Ronapa/Circuitos2/Imagenes/esquematico_margen_fase.PNG

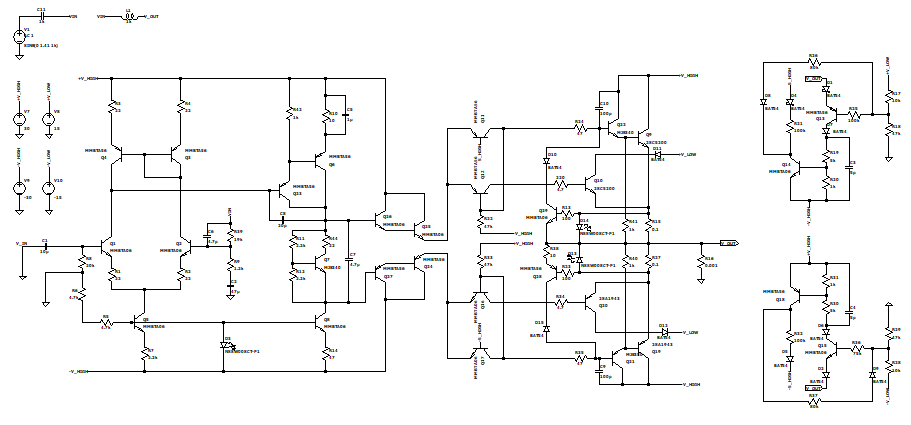
Imagenes/esquematico_margen_fase.PNG
