Ronapa/Circuitos2/Imagenes/grafico_compensacion.PNG

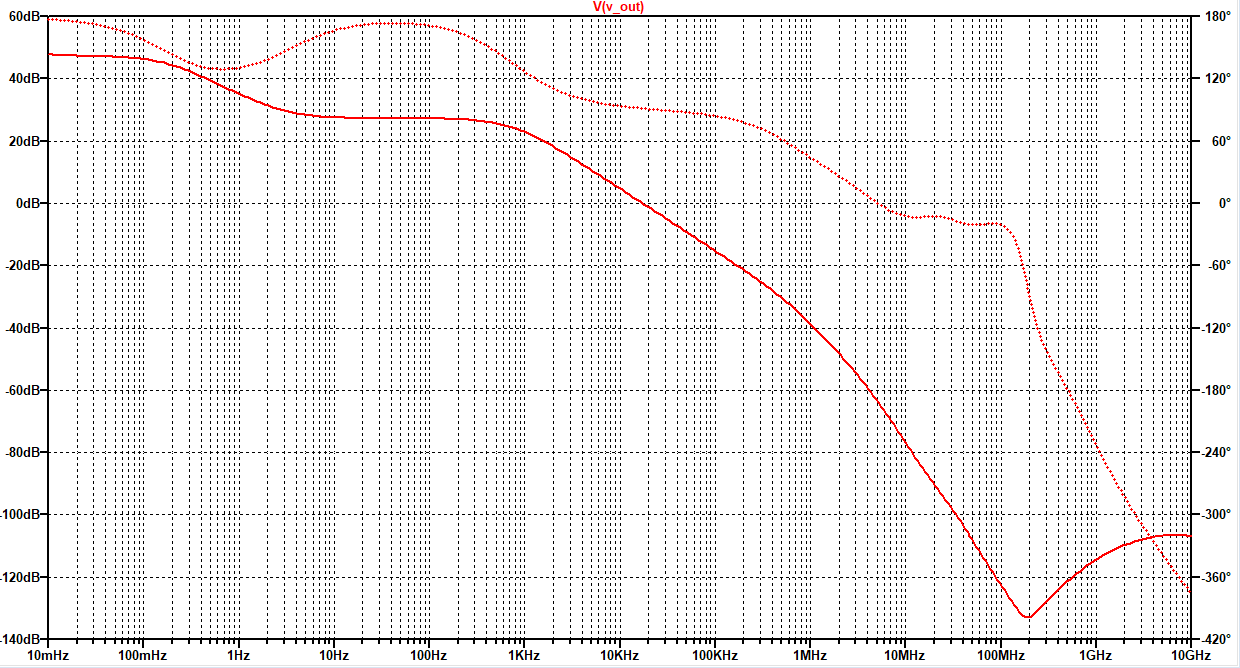
Imagenes/grafico_compensacion.PNG
