Ronapa/Circuitos2/Imagenes/Multiplicador_Vbe.PNG

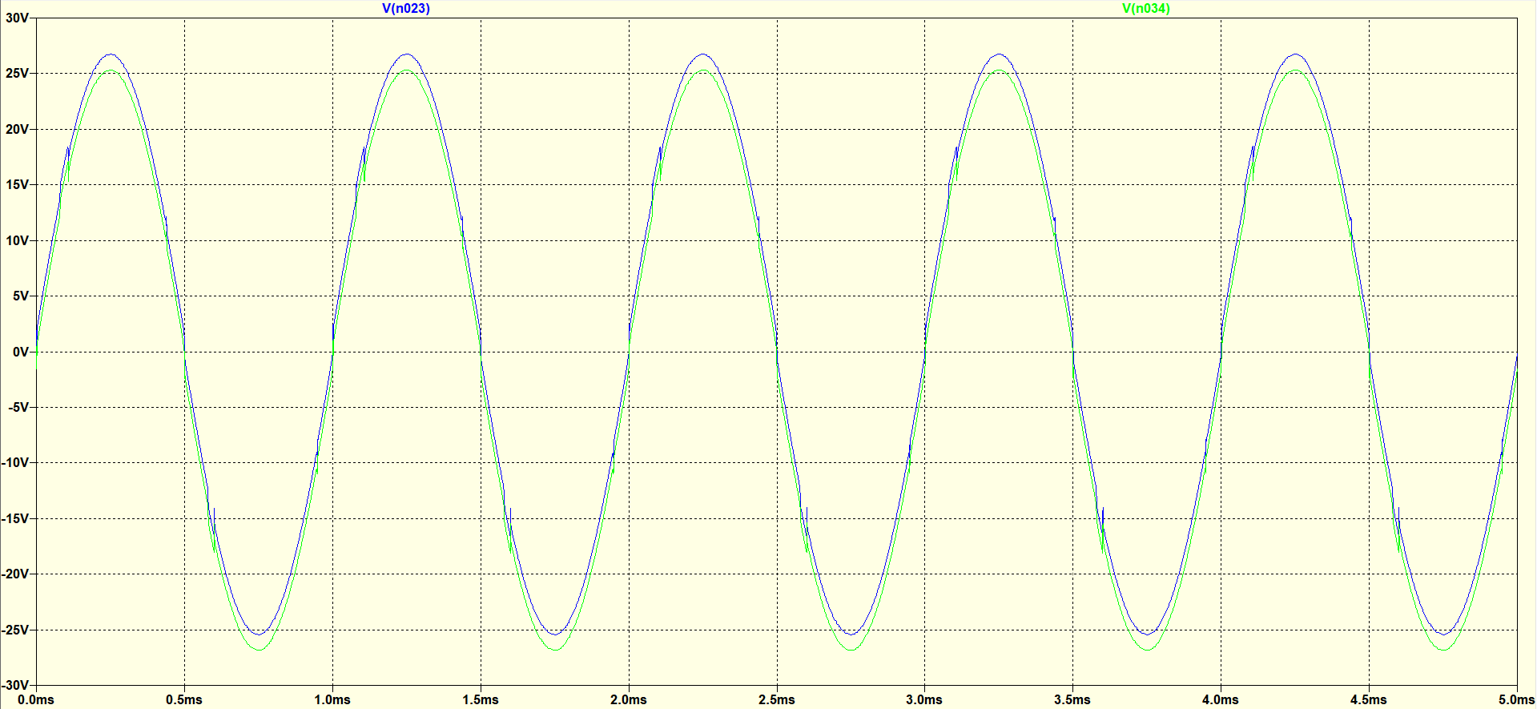
Imagenes/Multiplicador_Vbe.PNG
