Ronapa/Circuitos2/Imagenes/Tensión entrada.jpg

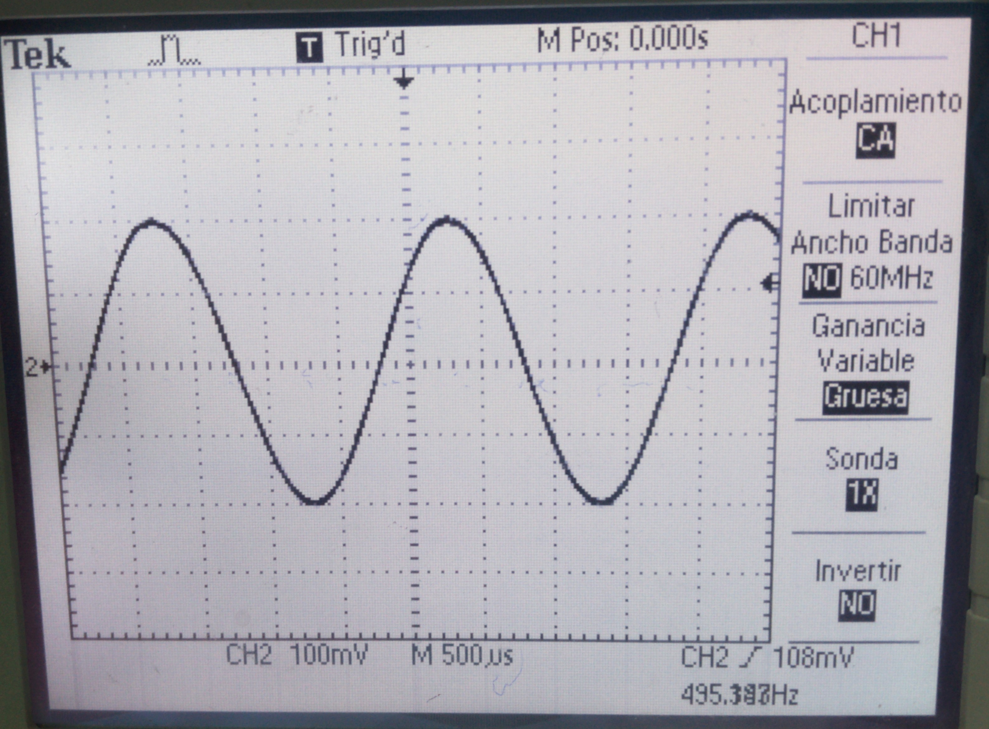
Imagenes/Tensión entrada.jpg
