Ronapa/Circuitos2/Imagenes/Tensión salida.jpg

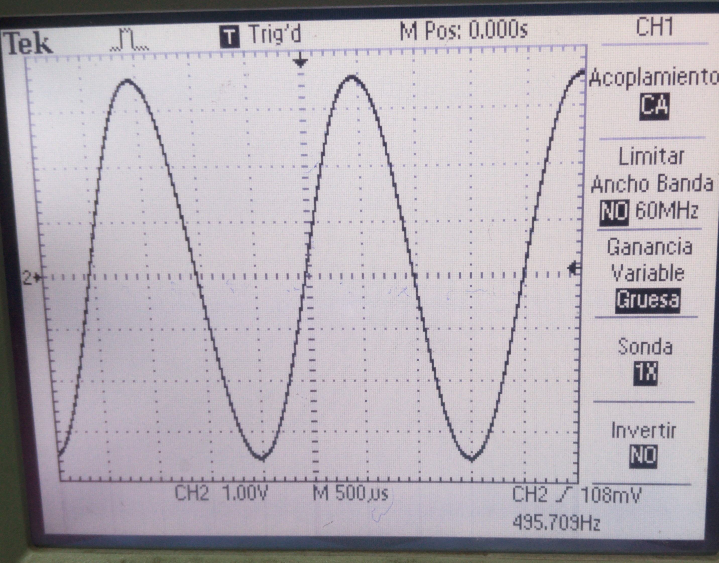
Imagenes/Tensión salida.jpg
