Ronapa/Circuitos2/PCB/Esquematico.PNG

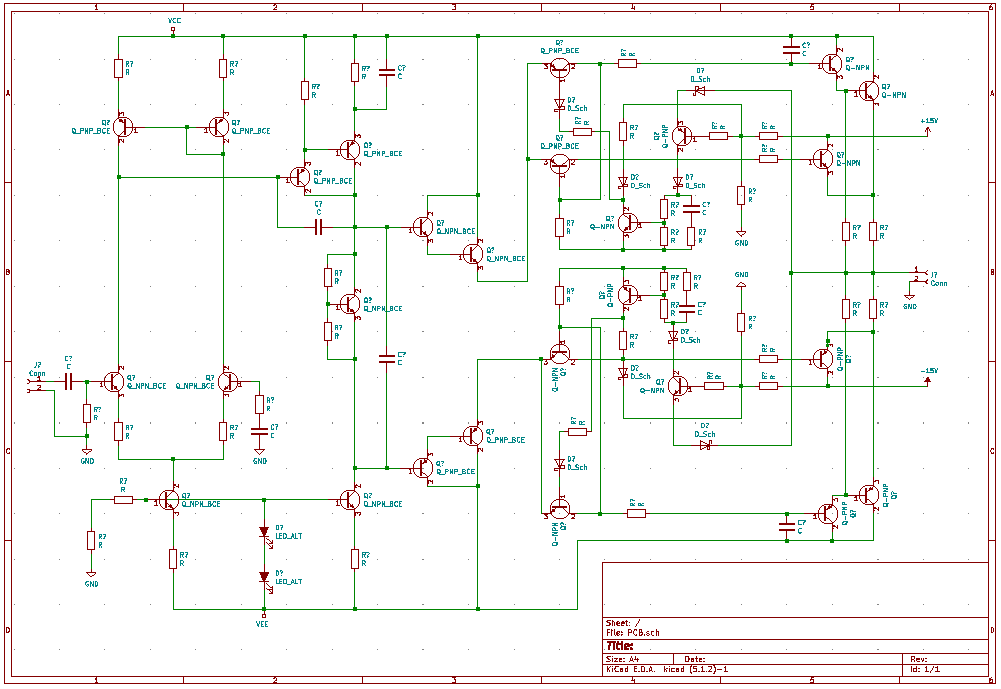
PCB/Esquematico.PNG
