Ronapa/Circuitos2/Simulaciones/fft 0.6V.PNG

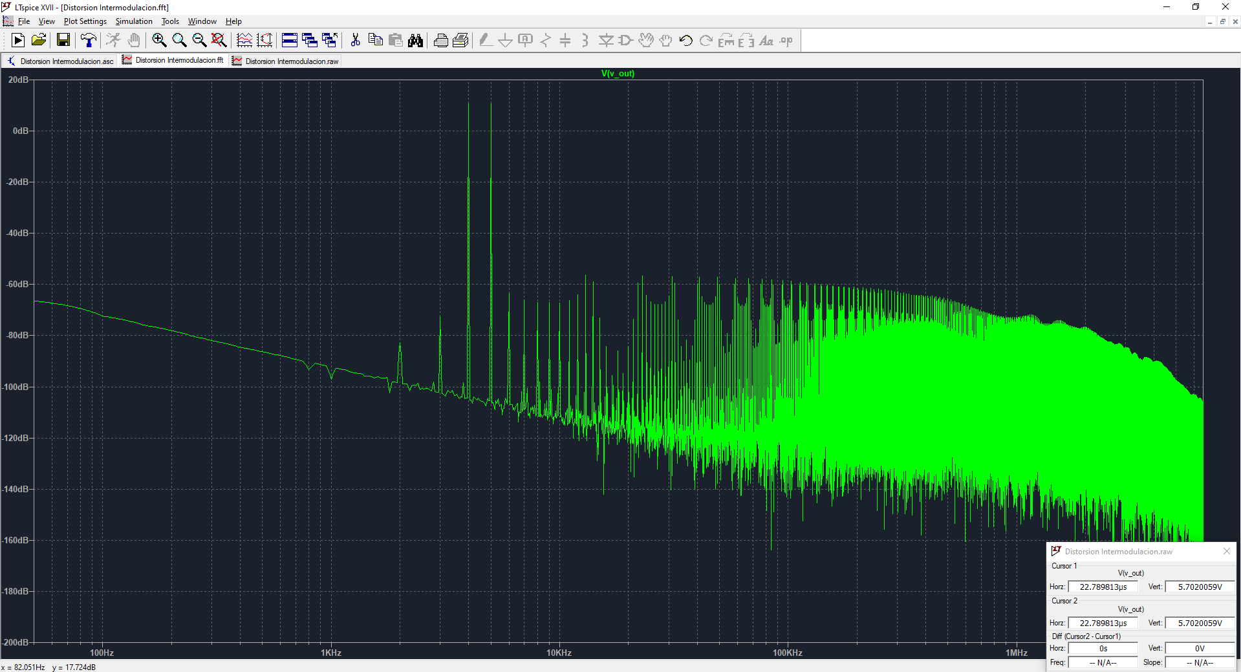
Simulaciones/fft 0.6V.PNG
