Ronapa/Circuitos2/Simulaciones/fft 1.4V 19 20k.PNG

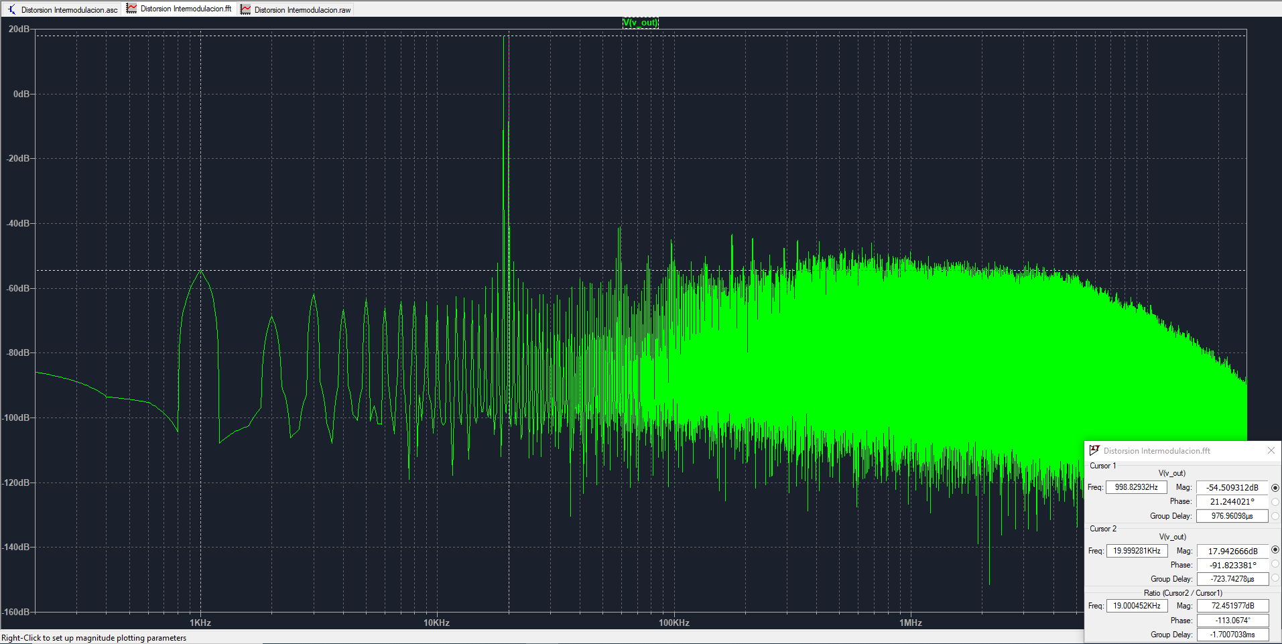
Simulaciones/fft 1.4V 19 20k.PNG
