Ronapa/Circuitos2/Simulaciones/fft 1.4V.PNG

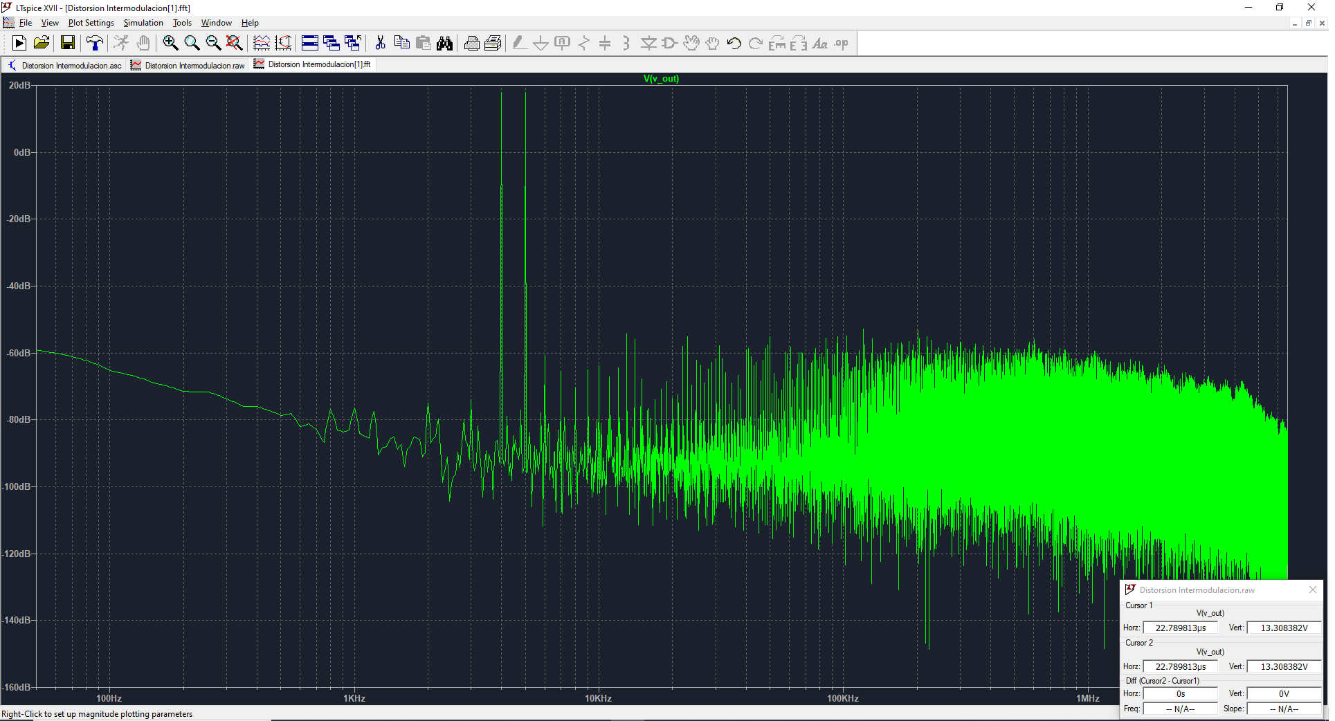
Simulaciones/fft 1.4V.PNG
