Ronapa/Circuitos2/LlaveElectronica.asc

Q1: npn
Q2: npn
Q3: pnp
Q4: pnp
R1: res; 10k
R2: res; 1k
R3: res; 10k
R4: res; 10k
V1: voltage; 20
V2: voltage; 20
V3: voltage; 5
V4: voltage; 6
Named nets: 0
.tran 1m
