Ronapa/Circuitos2/TP_PSNR.asc

220: res; 4.7
C1: cap; 10µ
C2: cap; 47µ
C3: cap; 5p
C4: cap; 5p
C5: cap; 1µ
C6: cap; 4.7p
C7: cap; 4.7µ
C8: cap; 20p
C9: cap; 330p
C10: cap; 330p
D1: schottky; BAT54
D2: diode; BAT54
D3: LED; NSSW008CT-P1
D4: schottky; BAT54
D5: diode; BAT54
D6: diode; BAT54
D7: diode; BAT54
D8: diode; BAT54
D9: diode; BAT54
D10: diode; BAT54
D11: diode; BAT54
D12: diode; BAT54
D13: LED; NSSW008CT-P1
D14: LED; NSSW008CT-P1
D15: diode; BAT54
Q1: npn; MMBTA06
Q2: npn; MMBTA06
Q3: pnp; MMBTA56
Q4: pnp; MMBTA56
Q5: npn; MMBTA06
Q6: pnp; MMBTA56
Q7: npn; MJE340
Q8: npn; MMBTA06
Q9: npn; 2SC5200
Q10: npn; 2SC5200
Q11: pnp; MMBTA56
Q12: pnp; MMBTA56
Q13: pnp; MMBTA56
Q14: npn; MMBTA06
Q15: npn; MMBTA06
Q16: npn; MMBTA06
Q17: npn; MMBTA06
Q18: pnp; MMBTA56
Q19: pnp; 2SA1943
Q20: pnp; 2SA1943
Q21: pnp; MJE350
Q22: npn; MJE340
Q23: pnp; MMBTA56
Q24: pnp; MMBTA56
Q25: npn; MMBTA06
Q26: npn; MMBTA06
Q27: pnp; MMBTA56
Q28: pnp; MMBTA56
Q29: npn; MMBTA06
R1: res; 22
R2: res; 22
R3: res; 22
R4: res; 22
R5: res; 4.7k
R6: res; 4.7k
R7: res; 2.2k
R8: res; 20k
R9: res; 1.2k
R10: res; 10
R11: res; 2.2k
R12: res; 2.2k
R13: res; 100
R14: res; 470
R15: res; 0.1
R16: res; 8
R17: res; 10k
R18: res; 47k
R19: res; 5k
R20: res; 1k
R21: res; 100k
R22: res; 47k
R23: res; 25
R24: res; 200
R25: res; 100k
R26: res; 80k
R27: res; 0.1
R28: res; 10k
R29: res; 47k
R30: res; 5k
R31: res; 1k
R32: res; 100k
R33: res; 47k
R34: res; 4.7
R35: res; 200
R36: res; 75k
R37: res; 80k
R39: res; 20k
R40: res; 1k
R41: res; 1k
R42: res; 1k
R44: res; 22
V3: voltage; SINE(0 0.5 1k 0); AC 1
V7: voltage; PULSE(30 31 0 19.5m 0.5m 0 20m)
V8: voltage; PULSE(15 15.5 0 19.5m 0.5m 0 20m)
V9: voltage; PULSE(-30 -31 0 19.5m 0.5m 0 20m)
V10: voltage; PULSE(-15 -15.5 0 19.5m 0.5m 0 20m)
Named nets: 0, +V_HIGH, +V_LOW, V_OUT, -V_HIGH, S_HIGH, -V_LOW, -S_HIGH, V_IN
.tran 0 700m 500m 1u
.FOUR 1khz 10 100 V(V_OUT)
.inc Librerias\\MJ2955.LIB
.inc Librerias\\2N3055.LIB
.inc Librerias\\2N5551.LIB
.inc Librerias\\2N5401.LIB
.inc Librerias\\1N4001.LIB
.MODEL BC850C NPN(
+ AF= 1.00E+00 BF= 3.20E+02 BR= 1.47E+01 CJC= 7.16E-12
+ CJE= 1.03E-11 CJS= 0.00E+00 EG= 1.11E+00 FC= 5.00E-01
+ IKF= 1.79E-01 IKR= 1.00E+00 IRB= 3.37E-03 IS= 3.71E-13
+ ISC= 1.71E-13 ISE= 2.77E-15 ITF= 2.26E+00 KF= 0.00E+00
+ MJC= 4.60E-01 MJE= 3.86E-01 MJS= 3.30E-01 NC= 1.21E+00
+ NE= 1.37E+00 NF= 1.14E+00 NR= 1.21E+00 PTF= 0.00E+00
+ RB= 1.00E+02 RBM= 1.00E+01 RC= 1.75E+00 RE= 1.00E-02
+ TF= 5.65E-10 TR= 0.00E+00 VAF= 2.49E+02 VAR= 3.31E+01
+ VJC= 3.00E-01 VJE= 3.00E-01 VJS= 7.50E-01 VTF= 9.99E+05
+ XCJC= 1.00E+00 XTB= 0.00E+00 XTF= 1.10E+02 XTI= 3.00E+00)
.MODEL BC860C PNP(
+ AF= 1.00E+00 BF= 1.72E+02 BR= 2.85E-02 CJC= 1.13E-11
+ CJE= 1.13E-10 CJS= 0.00E+00 EG= 1.11E+00 FC= 5.00E-01
+ IKF= 1.33E-01 IKR= 1.00E+00 IRB= 2.46E-03 IS= 1.63E-13
+ ISC= 7.42E-13 ISE= 4.39E-13 ITF= 2.78E+00 KF= 0.00E+00
+ MJC= 3.98E-01 MJE= 5.98E-01 MJS= 3.30E-01 NC= 1.52E+00
+ NE= 2.00E+00 NF= 1.06E+00 NR= 1.51E+00 PTF= 0.00E+00
+ RB= 5.00E+01 RBM= 1.00E+01 RC= 3.83E+00 RE= 1.00E-02
+ TF= 5.30E-10 TR= 0.00E+00 VAF= 2.68E+01 VAR= 1.00E+01
+ VJC= 3.00E-01 VJE= 7.38E-01 VJS= 7.50E-01 VTF= 9.99E+05
+ XCJC= 1.00E+00 XTB= 0.00E+00 XTF= 3.39E-01 XTI= 3.00E+00)
;ac dec 1000 10m 10000Meg
;op
.option numdgt=7
.inc Librerias\\MJE340.LIB
.inc Librerias\\MJE350.LIB
.inc Librerias\\MMBTA06.LIB
.inc Librerias\\MMBTA56.LIB
.option plotwinsize=0
.MODEL 2SC5200 npn IS=300f BF=100 NF=1 BR=8.025 NR=1.0 ISE=200p IKF=18 NE=2.0 ISC=2.01764E-10 NC=1.5 VAF=400 VAR=100 IKR=1.39087 RB=1.1 RBM=0.00011 IRB=1.51189E-6 RE=0.0032 RC=0.0183 CJE=6.1n VJE=0.711 MJE=0.304 FC=0.5 CJC=380p VJC=0.84 MJC=0.25 TF=5n TR=3.342E-7 XTB=1.72 EG=0.78 XTI=3
.MODEL 2SA1943 pnp IS=650f BF=100 NF=1 BR=8.805 NR=1.0 ISE=10p IKF=15 NE=2.0 ISC=2.01764E-10 NC=1.5 VAF=600 VAR=100 IKR=1.39087 RB=1.1 RBM=0.00011 IRB=1.51189E-9 RE=0.0061 RC=0.0103 CJE=5.26n VJE=0.711 MJE=0.304 FC=0.5 CJC=750p VJC=0.84 MJC=0.25 TF=5n TR=3.342E-7 XTB=2.28 EG=0.81 XTI=3
V(-V_LOW)*I(V10)+V(-V_HIGH)*I(V9)+V(+V_HIGH)*I(V7)+V(+V_LOW)*I(V8)
