Ronapa/Circuitos2/proteccion rele.asc

C1: cap; 22µ
D1: diode
D2: diode
D3: diode
D4: diode
L1: ind; 1m
Q1: npn
Q2: pnp
Q3: pnp
R1: res; 100k
R2: res; 10k
R3: res; 200k
R4: res; 2k
R5: res; 600
V1: voltage; 15v
V2: voltage; SINE(3 1 20); AC 1
Named nets: 0
.tran 1
;ac dec 1000 0.001 10
