Ronapa/Circuitos2/TPdisenio compensacion.asc

C1: cap; 2.2µ
C2: cap; 470µ
C3: cap; 150p
C4: cap; 150p
C5: cap; 1µ
C6: cap; 4.7p
C7: cap; 10µ
C8: cap; 20p
C9: cap; 1k
C10: cap; 22p
C11: cap; 22p
D1: schottky; BAT54
D2: diode; BAT54
D3: LED; NSSW008CT-P1
D4: schottky; BAT54
D5: diode; BAT54
D6: diode; BAT54
D7: diode; BAT54
D8: diode; BAT54
D9: diode; BAT54
L1: ind; 1k
Q1: npn; BC850C
Q2: npn; BC850C
Q3: pnp; BC860C
Q4: pnp; BC860C
Q5: npn; BC850C
Q6: pnp; MMBTA56
Q7: npn; MJE340
Q8: npn; MMBTA06
Q9: npn; 2N3055
Q10: npn; 2N3055
Q11: pnp; BC860C
Q12: pnp; BC860C
Q13: pnp; BC860C
Q14: npn; BC850C
Q15: npn; BC850C
Q16: npn; BC850C
Q17: npn; BC850C
Q18: pnp; BC860C
Q19: pnp; MJ2955
Q20: pnp; MJ2955
Q21: pnp; MJE350
Q22: npn; MJE340
Q23: pnp; MMBTA56
Q24: pnp; MMBTA56
Q25: npn; MMBTA06
Q26: npn; MMBTA06
Q27: pnp; MMBTA56
Q28: pnp; BC860C
Q29: npn; BC850C
R1: res; 22
R2: res; 22
R3: res; 22
R4: res; 22
R5: res; 4.7k
R6: res; 4.7k
R7: res; 2.2k
R8: res; 20k
R9: res; 1.2k
R10: res; 10
R11: res; 2.2k
R12: res; 2.2k
R13: res; 47
R14: res; 47
R15: res; 0.22
R16: res; 8
R17: res; 11k
R18: res; 43k
R19: res; 50k
R20: res; 15k
R21: res; 47k
R22: res; 47k
R23: res; 18
R24: res; 4.7
R25: res; 150k
R26: res; 80k
R27: res; 0.22
R28: res; 11k
R29: res; 43k
R30: res; 50k
R31: res; 15k
R32: res; 47k
R33: res; 47k
R34: res; 18
R35: res; 4.7
R36: res; 100k
R37: res; 80k
R38: res; 100
R39: res; 20k
R40: res; 1k
R41: res; 1k
R42: res; 1k
R43: res; 100
R44: res; 22
R45: res; 3.3k
R46: res; 3.3k
R47: res; 10k
V1: voltage; SINE(0 1.41 1k); AC 1
V7: voltage; 30
V8: voltage; 15
V9: voltage; -30
V10: voltage; -15
Named nets: 0, +V_HIGH, +V_LOW, V_OUT, -V_HIGH, S_HIGH, -V_LOW, -S_HIGH, VIN
;tran 0 1m 0m 100n
.FOUR 10khz V(V_OUT)
.inc MJ2955.LIB
.inc 2N3055.LIB
.inc 2N5551.LIB
.inc 2N5401.LIB
.inc 1N4001.LIB
.MODEL BC850C NPN(
+ AF= 1.00E+00 BF= 3.20E+02 BR= 1.47E+01 CJC= 7.16E-12
+ CJE= 1.03E-11 CJS= 0.00E+00 EG= 1.11E+00 FC= 5.00E-01
+ IKF= 1.79E-01 IKR= 1.00E+00 IRB= 3.37E-03 IS= 3.71E-13
+ ISC= 1.71E-13 ISE= 2.77E-15 ITF= 2.26E+00 KF= 0.00E+00
+ MJC= 4.60E-01 MJE= 3.86E-01 MJS= 3.30E-01 NC= 1.21E+00
+ NE= 1.37E+00 NF= 1.14E+00 NR= 1.21E+00 PTF= 0.00E+00
+ RB= 1.00E+02 RBM= 1.00E+01 RC= 1.75E+00 RE= 1.00E-02
+ TF= 5.65E-10 TR= 0.00E+00 VAF= 2.49E+02 VAR= 3.31E+01
+ VJC= 3.00E-01 VJE= 3.00E-01 VJS= 7.50E-01 VTF= 9.99E+05
+ XCJC= 1.00E+00 XTB= 0.00E+00 XTF= 1.10E+02 XTI= 3.00E+00)
.MODEL BC860C PNP(
+ AF= 1.00E+00 BF= 1.72E+02 BR= 2.85E-02 CJC= 1.13E-11
+ CJE= 1.13E-10 CJS= 0.00E+00 EG= 1.11E+00 FC= 5.00E-01
+ IKF= 1.33E-01 IKR= 1.00E+00 IRB= 2.46E-03 IS= 1.63E-13
+ ISC= 7.42E-13 ISE= 4.39E-13 ITF= 2.78E+00 KF= 0.00E+00
+ MJC= 3.98E-01 MJE= 5.98E-01 MJS= 3.30E-01 NC= 1.52E+00
+ NE= 2.00E+00 NF= 1.06E+00 NR= 1.51E+00 PTF= 0.00E+00
+ RB= 5.00E+01 RBM= 1.00E+01 RC= 3.83E+00 RE= 1.00E-02
+ TF= 5.30E-10 TR= 0.00E+00 VAF= 2.68E+01 VAR= 1.00E+01
+ VJC= 3.00E-01 VJE= 7.38E-01 VJS= 7.50E-01 VTF= 9.99E+05
+ XCJC= 1.00E+00 XTB= 0.00E+00 XTF= 3.39E-01 XTI= 3.00E+00)
.lib opamp.sub
.ac dec 1000 1 10Meg
;op
.option numdgt=7
.inc MJE340.LIB
.inc MJE350.LIB
.inc MMBTA06.LIB
.inc MMBTA56.LIB
.option plotwinsize=0
