Ronapa/Circuitos2/Salida clase G v01.asc

C1: cap; 15p
C2: cap; 15p
D1: diode; 1N4001
D3: diode; 1N4001
Q1: npn; 2N3055
Q2: npn; 2N3055
Q3: pnp; 2N5401
Q4: pnp; 2N5401
Q5: pnp; 2N5401
Q6: npn; 2N5551
Q13: npn; 2N5551
Q14: npn; 2N5551
Q15: npn; 2N5551
Q16: pnp; 2N5401
Q17: pnp; MJ2955
Q18: pnp; MJ2955
R1: res; 0.33
R2: res; 8
R3: res; 11k
R4: res; 43k
R5: res; 50k
R6: res; 15k
R7: res; 47k
R8: res; 47k
R9: res; 300k
R10: res; 18
R11: res; 18
R12: res; 150k
R13: res; 0.33
R15: res; 11k
R16: res; 43k
R17: res; 50k
R18: res; 15k
R19: res; 47k
R20: res; 47k
R21: res; 18
R22: res; 18
R23: res; 150k
R24: res; 300k
V1: voltage; 30
V2: voltage; 15
V3: voltage; -30
V4: voltage; -15
V5: voltage; SINE(0 29 1k)
Named nets: +V_HIGH, +V_LOW, 0, -V_HIGH, -V_LOW, V_OUT, S_HIGH, -S_HIGH
.tran 0 10m 0 1m
.FOUR 1khz 10 10 V(V_OUT)
.inc MJ2955.LIB
.inc 2N3055.LIB
.inc 2N5551.LIB
.inc 2N5401.LIB
.inc 1N4001.LIB
